Gepetto/MC300A_AS5047_encoder_PCB/encoder_PCB/3D Models/AS5047U-HTSM.stp

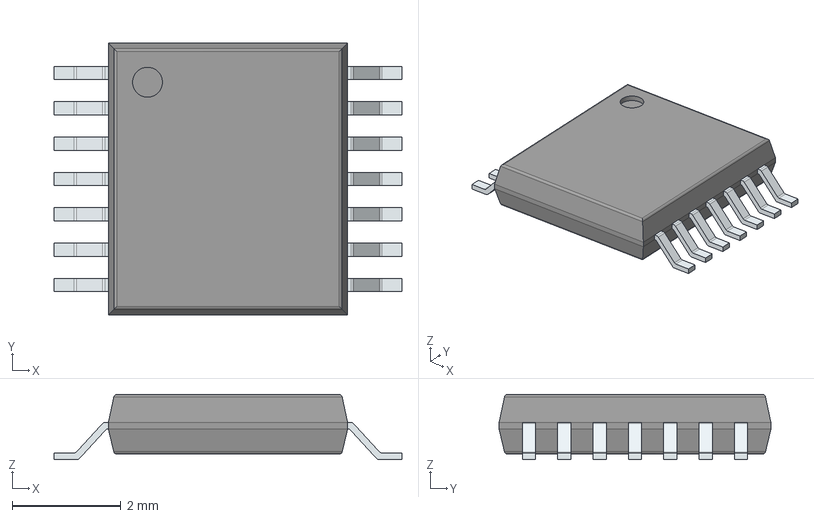
[picture p12: CAD file, 2022-05-24]
encoder_PCB/3D Models/AS5047U-HTSM.stp
6.40 x 5.00 x 1.20 mm
PinsArrayLR
